th-in-gs/SwitchDualShockAdapter/src/serial.cpp

#include <serial.h>
#include <avr/io.h>
#include <stdlib.h>
#include <packedStrings.h>

// A simple circular buffer to store serial output.
static const uint8_t sSerialOutputBufferLength = 128;
static uint8_t sSerialOutputBuffer[sSerialOutputBufferLength];
static uint8_t sSerialOutputBufferStart = 0;
static uint8_t sSerialOutputBufferEnd = 0;


void serialInit(const uint32_t baudRate)
{
    const uint16_t ubrr = (F_CPU + (baudRate * 4)) / (baudRate * 16) - 1;

#ifdef __AVR_ATmega8__
    UBRRH = (uint8_t)(ubrr >> 8);
    UBRRL = (uint8_t)ubrr;

    UCSRB = (1 << TXEN);
    UCSRC = (1 << URSEL) | (1 << UCSZ1) | (1 << UCSZ0);
#else
    UBRR0H = (uint8_t)(ubrr >> 8);
    UBRR0L = (uint8_t)ubrr;

    UCSR0B = (1 << TXEN0);
    UCSR0C = (1 << UCSZ01) | (1 << UCSZ00);
#endif
}

void serialPoll()
{
    if(sSerialOutputBufferStart != sSerialOutputBufferEnd) {
#ifdef __AVR_ATmega8__
        if(UCSRA & (1 << UDRE)) {
            UDR =
#else
        if(UCSR0A & (1 << UDRE0)) {
            UDR0 =
#endif
                sSerialOutputBuffer[sSerialOutputBufferStart];
            sSerialOutputBufferStart = (uint8_t)(sSerialOutputBufferStart + 1) % sSerialOutputBufferLength;
        }
    }
}

void serialPrint(const uint8_t ch, const bool wait)
{
    if(wait) {
        while(sSerialOutputBufferStart != sSerialOutputBufferEnd) {
            serialPoll();
        }
    }
    sSerialOutputBuffer[sSerialOutputBufferEnd] = ch;
    sSerialOutputBufferEnd = (uint8_t)(sSerialOutputBufferEnd + 1) % sSerialOutputBufferLength;
}

static void serialPrintNybble(const uint8_t nybble, const bool wait)
{
    serialPrint(nybble >= 0xA ? 'A' - 0xA + nybble : '0' + nybble, wait);
}

void serialPrintHex(uint8_t byte, const bool wait)
{
    serialPrintNybble(byte >> 4, wait);
    serialPrintNybble(byte & 0xF, wait);
}

void serialPrintHex16(uint16_t byte, const bool wait)
{
    serialPrintHex((uint8_t)(byte >> 8), wait);
    serialPrintHex((uint8_t)(byte), wait);
}

void serialPrintBuffer(const void *buffer, uint8_t length)
{
    const uint8_t *cursor = (const uint8_t *)buffer;
    const uint8_t *end = (const uint8_t *)buffer + length;
    for(; cursor < end;) {
        const uint8_t *lineEndCursor = cursor + 8;
        for(; cursor < end && cursor < lineEndCursor; ++cursor) {
            serialPrintHex(*cursor);
            serialPrint(' ');
        }
        serialPrint('\n');
    }
}

void serialPrintDec(const uint8_t ch, const bool wait)
{
    uint8_t toPrint = ch % 10;
    uint8_t remaining = ch / (uint8_t)10;
    if(remaining) {
        serialPrintDec(remaining, wait);
    }
    serialPrint('0' + toPrint, wait);
}

/*void serialPrint(const char *string, const bool wait)
{
    uint8_t ch;
    do {
        ch = *string;
        if(ch) {
            serialPrint(ch, wait);
            ++string;
        }
    } while(ch != 0);
}*/

void serialPrintStr6(const uint8_t *str6, const bool wait)
{
    uint8_t ch;
    uint8_t i = 0;
    do {
        ch = str6CharAtIndex(str6, i);
        if(ch) {
            serialPrint(ch, wait);
            ++i;
        }
    } while(ch != 0);
}
