th-in-gs/SwitchDualShockAdapter/src/spiMemory.h

#ifndef __spimemory_h_included__
#define __spimemory_h_included__

#include <stdint.h>
#include <avr/pgmspace.h>

bool spiMemoryRead(uint8_t *out, uint16_t address, uint16_t length);
bool spiMemoryWrite(uint16_t address, const uint8_t *buffer, uint16_t length);

#endif
